AleksaHeler/FlexNode/Node/NodeSoftware/sensor_pcb_temp.h

#ifndef SENSOR_PCB_TEMP_H
#define SENSOR_PCB_TEMP_H

/* System includes */
#include <ArduinoJson.h>
#include "generic_driver.h"

/* Create a class for this sensor */
class PcbTempSensor : public Driver
{
protected:
  #define NUM_OF_NTC_LOOKUPS 124 /* How many lookup values we have */
  uint8_t sensor_pin;
  float system_pcb_temp = 0;

  /* Custom struct to hold lookup values */
  typedef struct ntc_lookup_struct {
    float temperature;
    uint16_t raw_adc;
  };

  const ntc_lookup_struct ntc_lookup_values[NUM_OF_NTC_LOOKUPS] = {
    { -23, 298 }, 
    { -22, 316 }, 
    { -21, 335 }, 
    { -20, 354 }, 
    { -19, 375 }, 
    { -18, 396 }, 
    { -17, 418 }, 
    { -16, 441 }, 
    { -15, 465 }, 
    { -14, 490 }, 
    { -13, 516 }, 
    { -12, 543 }, 
    { -11, 571 }, 
    { -10, 600 }, 
    {  -9, 629 }, 
    {  -8, 660 }, 
    {  -7, 692 }, 
    {  -6, 724 }, 
    {  -5, 758 }, 
    {  -4, 792 }, 
    {  -3, 827 }, 
    {  -2, 864 }, 
    {  -1, 901 }, 
    {   0, 938 }, 
    {   1, 977 }, 
    {   2, 1017 }, 
    {   3, 1057 }, 
    {   4, 1098 }, 
    {   5, 1140 }, 
    {   6, 1182 }, 
    {   7, 1225 }, 
    {   8, 1268 }, 
    {   9, 1312 }, 
    {  10, 1357 }, 
    {  11, 1402 }, 
    {  12, 1447 }, 
    {  13, 1493 }, 
    {  14, 1539 }, 
    {  15, 1585 }, 
    {  16, 1631 }, 
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
  };

public:
  /*****************************************************/
  /* Constructor                                       */
  /*****************************************************/
  PcbTempSensor(uint8_t l_pin)
  {
    sensor_pin = l_pin;
  }

  /*****************************************************/
  /* Init function                                     */
  /*****************************************************/
  void Init()
  {
    pinMode(sensor_pin, INPUT);
  }

  /*****************************************************/
  /* Handle function                                   */
  /*****************************************************/
  void Handle(JsonDocument *json_message)
  {
    system_pcb_temp = calculate_pcb_temp(analogRead(sensor_pin));
    (*json_message)["pcb_temp"] = system_pcb_temp;
  }

  /*****************************************************/
  /* Helper functions                                  */
  /*****************************************************/
  
  /* Convert raw ADC value from a 10k NTC thermistor (connected to 3.3V on one side, and on another via 10k pulldown to GND) */
  float calculate_pcb_temp(float raw_adc)
  {
    uint16_t i = 0;

    /* Assume the first one is the best */
    uint16_t closest_adc = ntc_lookup_values[0].raw_adc;
    uint16_t closest_temp = ntc_lookup_values[0].temperature;

    /* Go over all... */
    for(i = 1; i < NUM_OF_NTC_LOOKUPS; i++)
    {
      /* If there's a new closest value found */
      if(abs(ntc_lookup_values[i].raw_adc - raw_adc) < abs(closest_adc - raw_adc))
      {
        /* Memorize it */
        closest_adc = ntc_lookup_values[i].raw_adc;
        closest_temp = ntc_lookup_values[i].temperature;
      }
    }
    
    /* For now, just return the closest temperature found (later we shall interpolate for precision) */
    return closest_temp;
  }
};

#endif /* #ifndef SENSOR_PCB_TEMP_H */
